kalanagunathilaka/Smart-Ventilator/Smart Ventilator/USART.h

#ifndef USART_H_
#define USART_H_
#include <avr/io.h>							/* Include AVR std. library file */
#define BAUD_PRESCALE (((F_CPU / (BAUDRATE * 16UL))) - 1)	/* Define prescale value */

char USART_BUFFER[500] = "";
char data[150]; // GSM Data Buffer
void USART_Init(unsigned long BAUDRATE)				/* USART initialize function */
{
	UCSRB |= (1 << RXEN) | (1 << TXEN) | (1 << RXCIE);	/* Enable USART transmitter and receiver */
	UCSRC |= (1 << URSEL)| (1 << UCSZ0) | (1 << UCSZ1);	/* Write USCRC for 8 bit data and 1 stop bit */
	UBRRL = BAUD_PRESCALE;							/* Load UBRRL with lower 8 bit of prescale value */
	UBRRH = (BAUD_PRESCALE >> 8);					/* Load UBRRH with upper 8 bit of prescale value */
}
void USART_TxChar(char data)						/* Data transmitting function */
{
	UDR = data;										/* Write data to be transmitting in UDR */
	while (!(UCSRA & (1<<UDRE)));					/* Wait until data transmit and buffer get empty */
}

void USART_SendString(char *str)					/* Send string of USART data function */
{
	int i=0;
	while (str[i]!=0)
	{
		USART_TxChar(str[i]);						/* Send each char of string till the NULL */
		i++;
	}
}




#endif /* USART_H_ */
